blfuentes/Equili-bot-ista/Control/course/05-servo/schema/05-servo-schema_schem.png

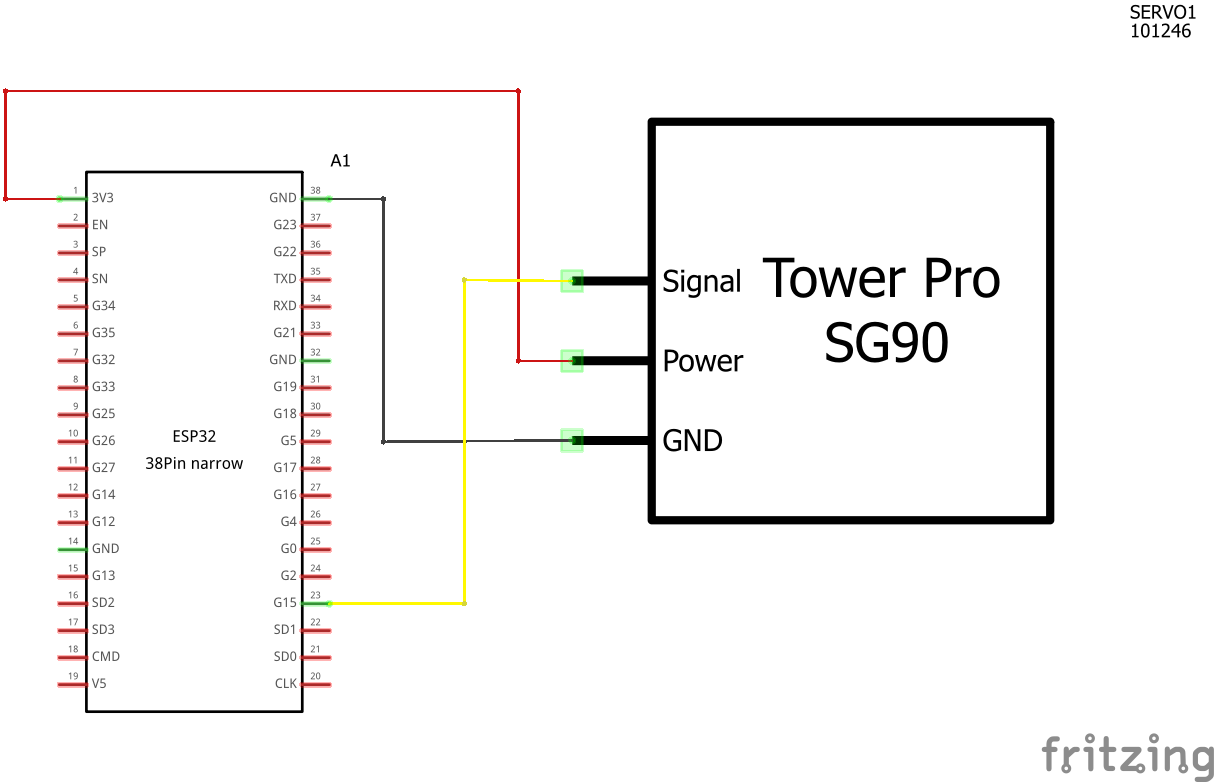
Control/course/05-servo/schema/05-servo-schema_schem.png
