blfuentes/Equili-bot-ista/Control/course/06-motor-driver/schema/06-motor-driver_schem.png

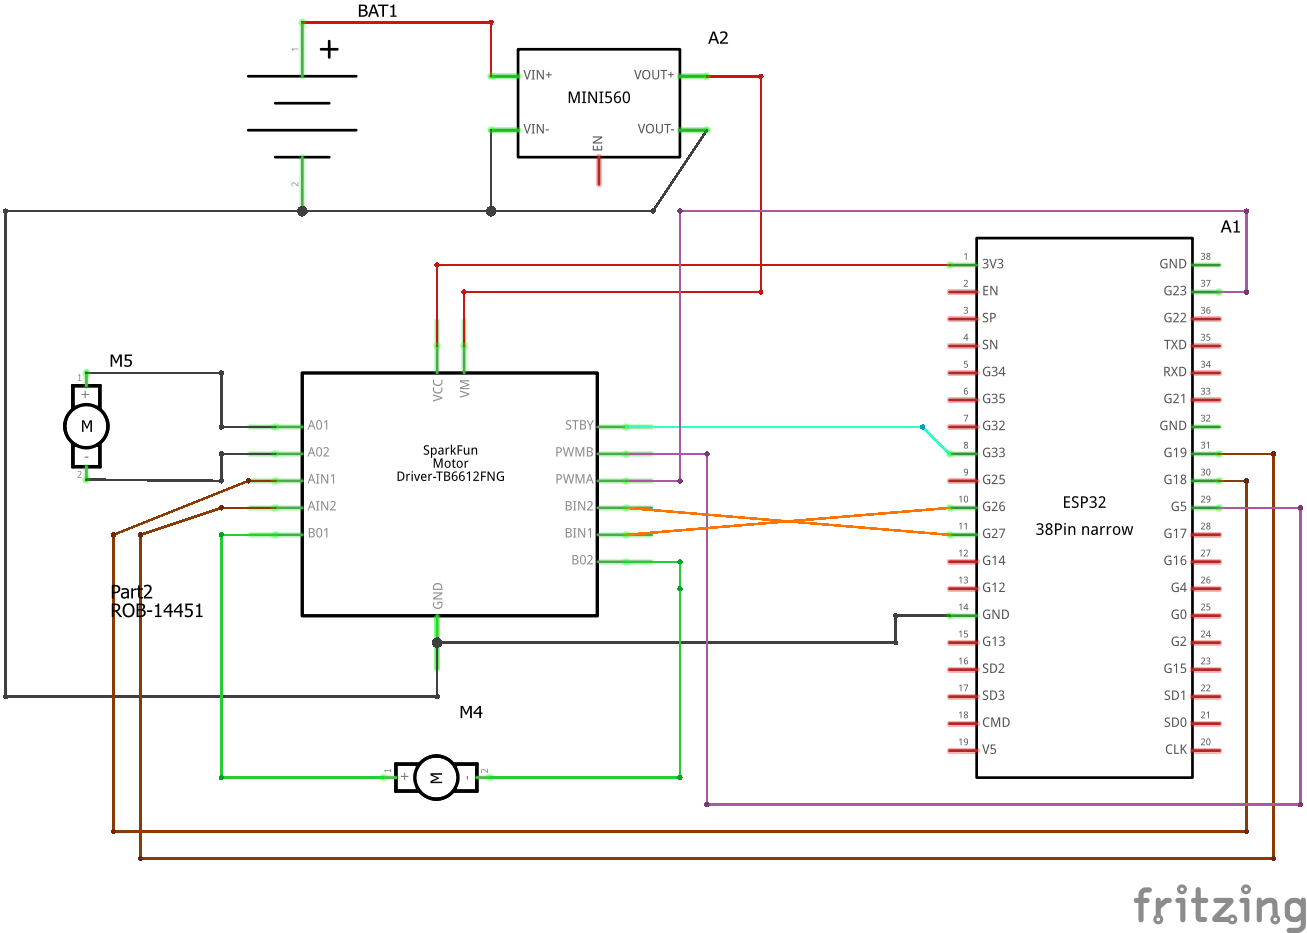
Control/course/06-motor-driver/schema/06-motor-driver_schem.png
